Cschaefer732/mini-rack-cluster/cad/tray-v1/views/iso_assembly_rear.png

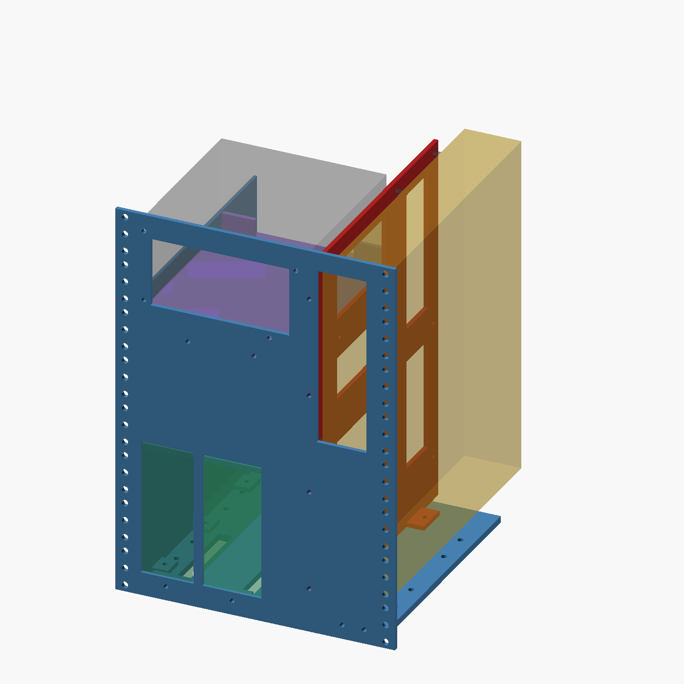
cad/tray-v1/views/iso_assembly_rear.png
